FedericoCampanelliPoli/V-SoM/PCB/Ethernet.kicad_sch

## KiCad design PCB/Ethernet.kicad_sch (2026-02-23)

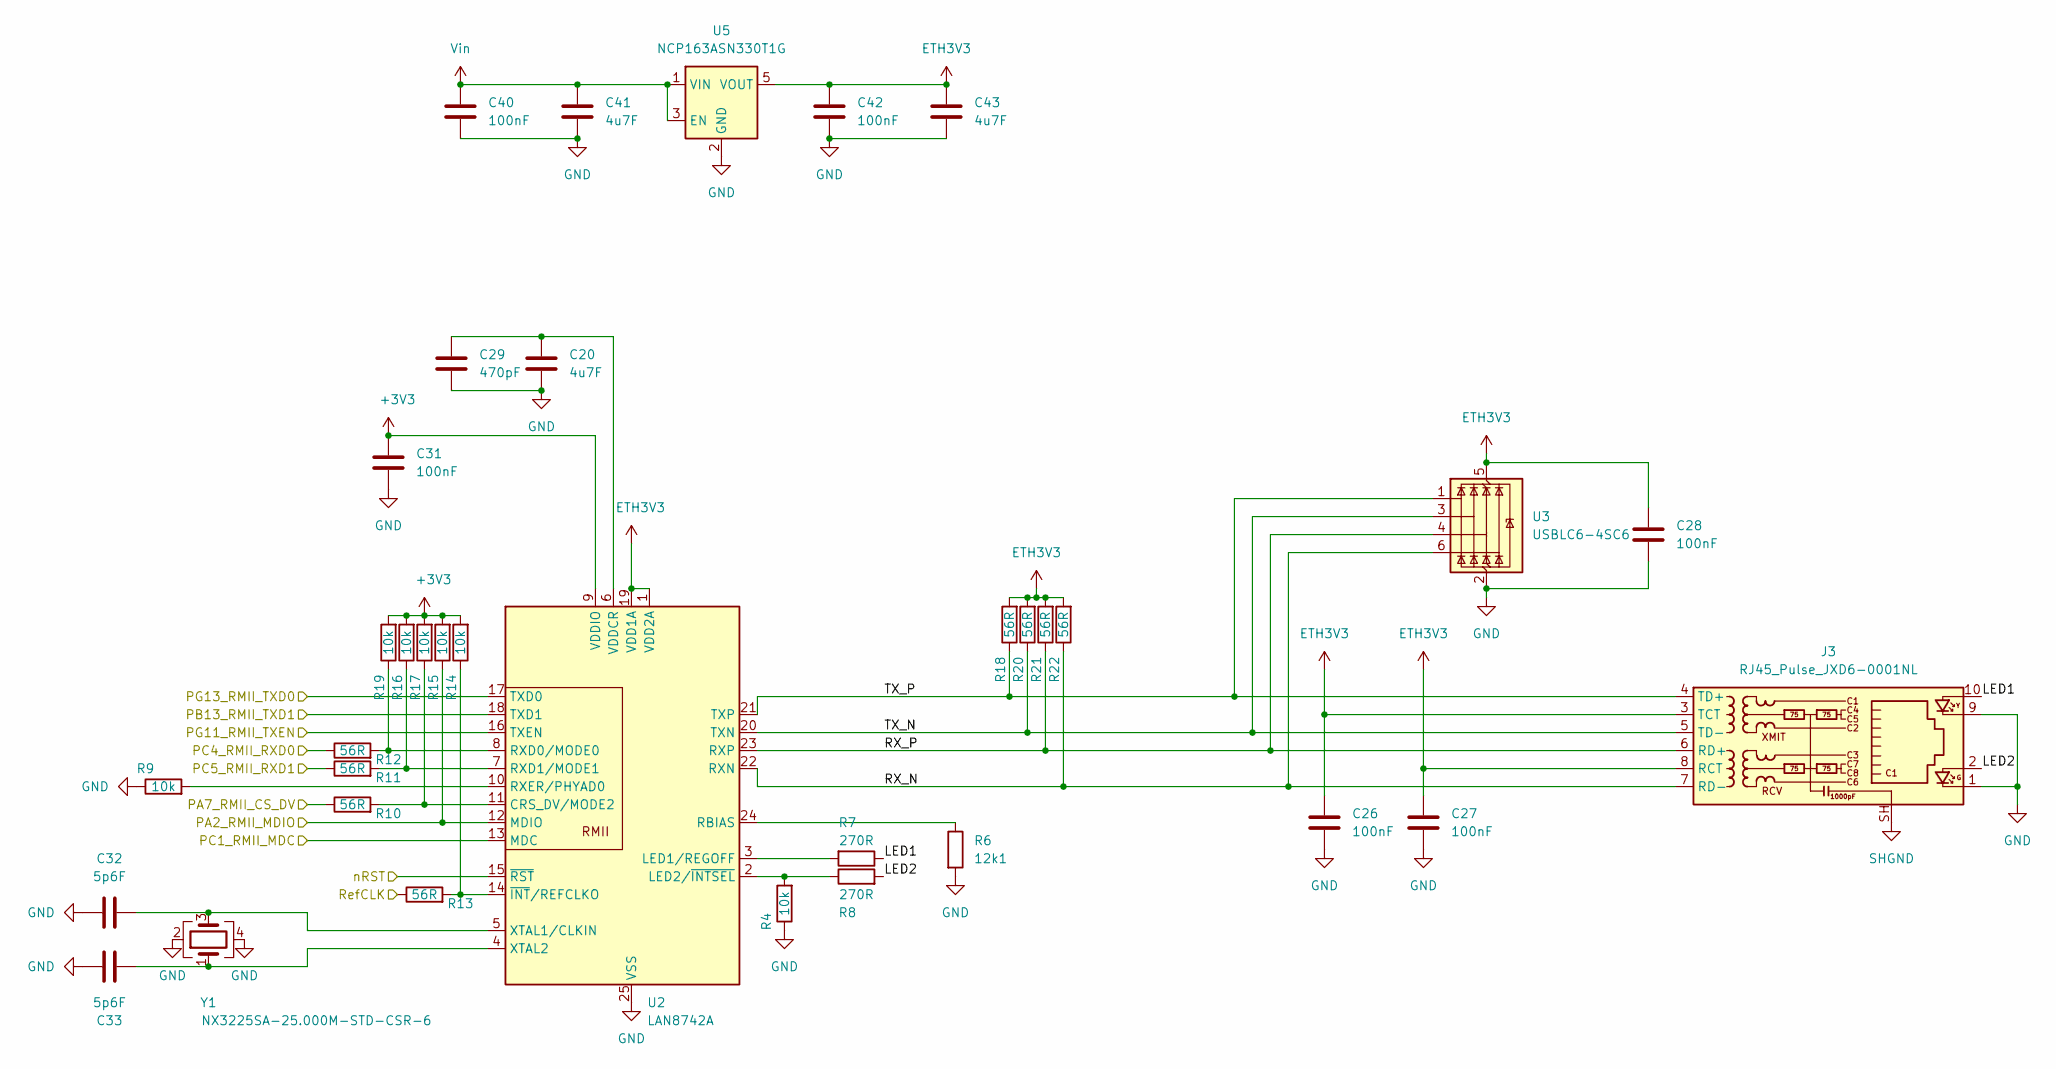
[picture p5: schematic Ethernet.kicad_sch]

Parts:
C20, C41, C43: 4u7F; C_0603_1608Metric; Manufacturer_Part_Number GRM188R61E475KE11D; Digikey PartNumber 490-7203-1-ND
C26, C27, C28, C31, C40, C42: 100nF; C_0603_1608Metric; Manufacturer_Part_Number C0603C104K5RACTU; Digikey PartNumber 399-C0603C104K5RACTUCT-ND
C29: 470pF; C_0603_1608Metric; Manufacturer_Part_Number C0603C471K5RACTU; Digikey PartNumber 399-C0603C471K5RACTUCT-ND
C32, C33: 5p6F; C_0603_1608Metric; Manufacturer_Part_Number C0603C569C5GACTU; Digikey PartNumber 399-C0603C569C5GACTUCT-ND
J3: RJ45_Pulse_JXD6-0001NL; RJ45_Pulse_JXD6-0001NL_Horizontal; Manufacturer_Part_Number JXD6-0001NL; Digikey PartNumber 553-JXD6-0001NLTCT-ND
R4, R9, R14, R15, R16, R17, R19: 10k; R_0603_1608Metric; Manufacturer_Part_Number RC0603FR-0710KL; Digikey PartNumber 311-10.0KHRCT-ND
R6: 12k1; R_0603_1608Metric; Manufacturer_Part_Number CRCW060312K1FKEAC; Digikey PartNumber 541-5158-1-ND
R7, R8: 270R; R_0603_1608Metric; Manufacturer_Part_Number RMCF0603FT270R; Digikey PartNumber RMCF0603FT270RCT-ND
R10, R11, R12, R13, R18, R20, R21, R22: 56R; R_0603_1608Metric; Manufacturer_Part_Number RC0603FR-0756RL; Digikey PartNumber 311-56.0HRCT-ND
U2: LAN8742A; VQFN-24-1EP_4x4mm_P0.5mm_EP2.5x2.5mm; Manufacturer_Part_Number LAN8742A-CZ; Digikey PartNumber LAN8742A-CZ-ND
U3: USBLC6-4SC6; SOT-23-6; Manufacturer_Part_Number USBLC6-4SC6; Digikey PartNumber 497-4492-1-ND
U5: NCP163ASN330T1G; SOT-23-5; Manufacturer_Part_Number NCP163ASN330T1G; Digikey PartNumber NCP163ASN330T1GOSCT-ND
Y1: NX3225SA-25.000M-STD-CSR-6; Oscillator_SMD_Abracon_ASE-4Pin_3.2x2.5mm; Manufacturer_Part_Number NX3225SA-25.000M-STD-CSR-6; Digikey PartNumber 644-STDCQR1-25MCT-ND

Connections:
+3V3: C31.1, R14.2, R15.2, R16.2, R17.2, R19.2, U2.9 (VDDIO)
ETH3V3: C26.1, C27.1, C28.1, C42.1, C43.1, J3.3 (TCT), J3.8 (RCT), R18.2, R20.2, R21.2, R22.2, U2.1 (VDD2A), U2.19 (VDD1A), U3.5 (VBUS), U5.5 (VOUT)
GND: C20.2, C26.2, C27.2, C28.2, C29.2, C31.2, C32.2, C33.2, C40.2, C41.2, C42.2, C43.2, J3.1, J3.9, R4.1, R6.2, R9.1, U2.25 (VSS), U3.2 (GND), U5.2 (GND), Y1.2, Y1.4
LED1: J3.10, R7.1
LED2: J3.2, R8.2
unnamed: C20.1, C29.1, U2.6 (VDDCR)
unnamed: C32.1, U2.5 (XTAL1/CLKIN), Y1.3
unnamed: C33.1, U2.4 (XTAL2), Y1.1
unnamed: R4.2, R8.1, U2.2 (LED2/~INTSEL)
unnamed: R6.1, U2.24 (RBIAS)
unnamed: R7.2, U2.3 (LED1/REGOFF)
unnamed: R9.2, U2.10 (RXER/PHYAD0)
unnamed: R10.2, R17.1, U2.11 (CRS_DV/MODE2)
unnamed: R11.2, R16.1, U2.7 (RXD1/MODE1)
unnamed: R12.2, R19.1, U2.8 (RXD0/MODE0)
unnamed: R13.2, R14.1, U2.14 (~INT/REFCLKO)
PA2_RMII_MDIO: R15.1, U2.12 (MDIO)
PA7_RMII_CS_DV: R10.1
PB13_RMII_TXD1: U2.18 (TXD1)
PC1_RMII_MDC: U2.13 (MDC)
PC4_RMII_RXD0: R12.1
PC5_RMII_RXD1: R11.1
PG11_RMII_TXEN: U2.16 (TXEN)
PG13_RMII_TXD0: U2.17 (TXD0)
RX_N: J3.7 (RD-), R22.1, U2.22 (RXN), U3.6 (I/O4)
RX_P: J3.6 (RD+), R21.1, U2.23 (RXP), U3.4 (I/O3)
RefCLK: R13.1
SHGND: J3.SH
TX_N: J3.5 (TD-), R20.1, U2.20 (TXN), U3.3 (I/O2)
TX_P: J3.4 (TD+), R18.1, U2.21 (TXP), U3.1 (I/O1)
Vin: C40.1, C41.1, U5.1 (VIN), U5.3 (EN)
nRST: U2.15 (~RST)
