FedericoCampanelliPoli/V-SoM/PCB/Power_Supply.kicad_sch

## KiCad design PCB/Power_Supply.kicad_sch (2026-02-23)

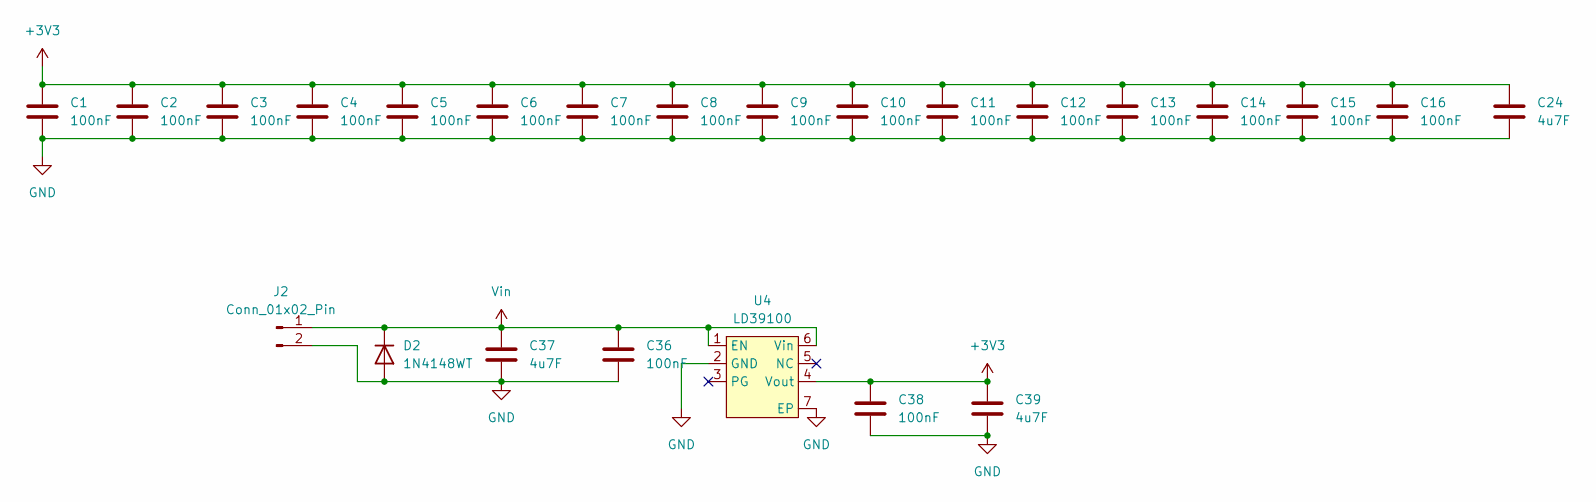
[picture p6: schematic Power_Supply.kicad_sch]

Parts:
C1, C2, C3, C4, C5, C6, C7, C8, C9, C10, C11, C12, C13, C14, C15, C16, C36, C38: 100nF; C_0603_1608Metric; Manufacturer_Part_Number C0603C104K5RACTU; Digikey PartNumber 399-C0603C104K5RACTUCT-ND
C24, C37, C39: 4u7F; C_0603_1608Metric; Manufacturer_Part_Number GRM188R61E475KE11D; Digikey PartNumber 490-7203-1-ND
D2: 1N4148WT; D_SOD-523; Manufacturer_Part_Number 1N4148WT; Digikey PartNumber 1N4148WTCT-ND
J2: Conn_01x02_Pin; PinHeader_1x02_P1.00mm_Vertical_SMD_Pin1Left; Manufacturer_Part_Number BC032-02-A-2-0200-0200-L-B; Digikey PartNumber 2073-BC032-02-A-2-0200-0200-L-BCT-ND
U4: LD39100; Maxim_TDFN-6-1EP_3x3mm_P0.95mm_EP1.5x2.3mm; Manufacturer_Part_Number LD39100PU33R; Digikey PartNumber 497-17047-1-ND

Connections:
+3V3: C1.1, C2.1, C3.1, C4.1, C5.1, C6.1, C7.1, C8.1, C9.1, C10.1, C11.1, C12.1, C13.1, C14.1, C15.1, C16.1, C24.1, C38.1, C39.1, U4.4 (Vout)
GND: C1.2, C2.2, C3.2, C4.2, C5.2, C6.2, C7.2, C8.2, C9.2, C10.2, C11.2, C12.2, C13.2, C14.2, C15.2, C16.2, C24.2, C36.2, C37.2, C38.2, C39.2, D2.2 (A), J2.2, U4.2 (GND), U4.7 (EP)
Vin: C36.1, C37.1, D2.1 (K), J2.1, U4.1 (EN), U4.6 (Vin)
