FedericoCampanelliPoli/V-SoM/PCB/uC.kicad_sch

## KiCad design PCB/uC.kicad_sch (2026-02-23)

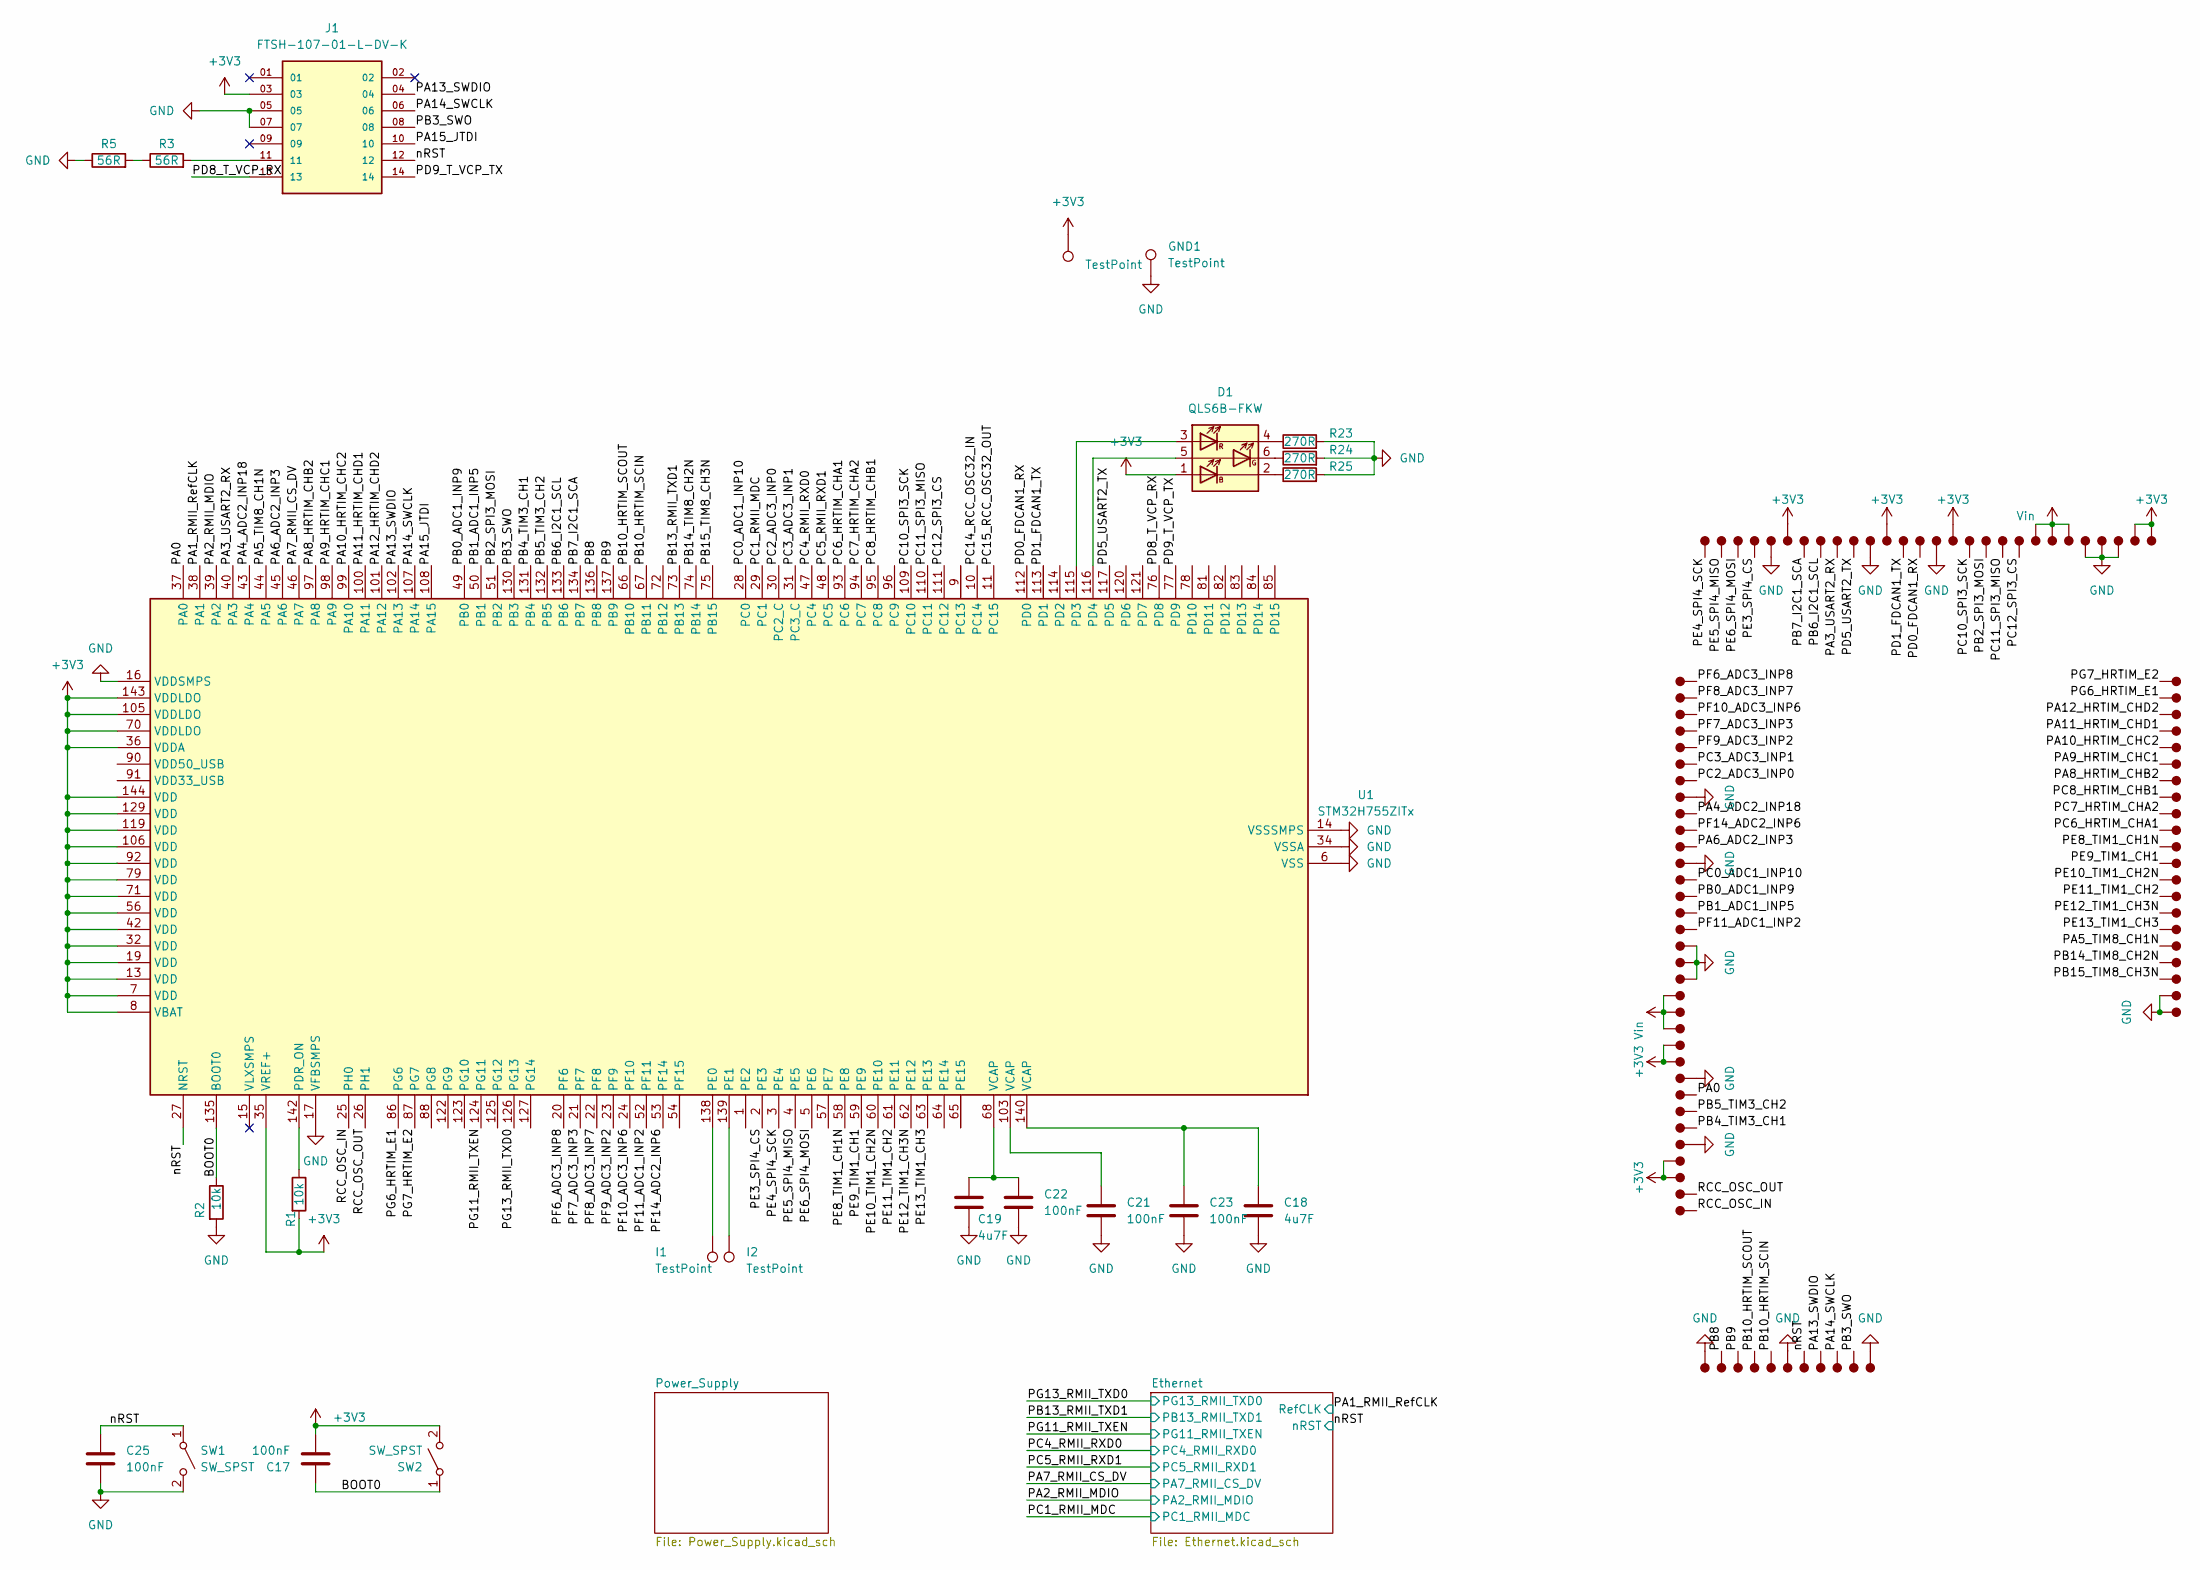
[picture p7: schematic uC.kicad_sch]

Parts:
3V3: TestPoint; TestPoint_Pad_D1.0mm; Manufacturer_Part_Number NA
C17, C21, C22, C23, C25: 100nF; C_0603_1608Metric; Manufacturer_Part_Number C0603C104K5RACTU; Digikey PartNumber 399-C0603C104K5RACTUCT-ND
C18, C19: 4u7F; C_0603_1608Metric; Manufacturer_Part_Number GRM188R61E475KE11D; Digikey PartNumber 490-7203-1-ND
D1: QLS6B-FKW; LED_Cree-PLCC6_4.7x1.5mm; Manufacturer_Part_Number QLS6B-FKW-CNSNSF043; Digikey PartNumber QLS6B-FKW-CNSNSF043CT-ND
GND1: TestPoint; TestPoint_Pad_D1.0mm; Manufacturer_Part_Number NA
I1, I2: TestPoint; TestPoint_Pad_D1.0mm; Manufacturer_Part_Number NA
J1: FTSH-107-01-L-DV-K; SAMTEC_FTSH-107-01-L-DV-K; PARTREV R; Digikey PartNumber SAM9449-ND
R1, R2: 10k; R_0603_1608Metric; Manufacturer_Part_Number RC0603FR-0710KL; Digikey PartNumber 311-10.0KHRCT-ND
R3, R5: 56R; R_0603_1608Metric; Manufacturer_Part_Number RC0603FR-0756RL; Digikey PartNumber 311-56.0HRCT-ND
R23, R24, R25: 270R; R_0603_1608Metric; Manufacturer_Part_Number RMCF0603FT270R; Digikey PartNumber RMCF0603FT270RCT-ND
SW1, SW2: SW_SPST; SW_Push_1P1T_NO_Vertical_Wuerth_434133025816; Manufacturer_Part_Number 434133025816; Digikey PartNumber 732-13663-1-ND
U1: STM32H755ZITx; LQFP-144_20x20mm_P0.5mm; Manufacturer_Part_Number STM32H755ZIT6; Digikey PartNumber STM32H755ZIT6-ND
U6, U7, U8, U9, U10, U11, U12, U13, U14, U15, U16, U17, U18, U19, U20, U21, U22, U23, U24, U25, U26, U27, U28, U29, U30, U31, U32, U33, U34, U35, U36, U37, U38, U39, U40, U41, U42, U43, U44, U45, U46, U47, U48, U49, U50, U51, U52, U53, U54, U55, U56, U57, U58, U59, U60, U61, U62, U63, U64, U65, U66, U67, U68, U69, U70, U71, U72, U73, U74, U75, U76, U77, U78, U79, U80, U81, U82, U83, U84, U85, U86, U87, U88, U89, U90, U91, U92, U93, U94, U95, U96, U97, U98: Castellation

Connections:
+3V3: 3V3.1, C17.2, D1.1 (AB), J1.03, R1.2, SW2.2 (B), U1.7 (VDD), U1.8 (VBAT), U1.13 (VDD), U1.19 (VDD), U1.32 (VDD), U1.35 (VREF+), U1.36 (VDDA), U1.42 (VDD), U1.56 (VDD), U1.70 (VDDLDO), U1.71 (VDD), U1.79 (VDD), U1.92 (VDD), U1.105 (VDDLDO), U1.106 (VDD), U1.119 (VDD), U1.129 (VDD), U1.143 (VDDLDO), U1.144 (VDD), U42.1, U45.1, U46.1, U48.1, U49.1, U53.1, U54.1, U55.1, U56.1
BOOT0: C17.1, R2.1, SW2.1 (A), U1.135 (BOOT0)
GND: C18.2, C19.2, C21.2, C22.2, C23.2, C25.2, GND1.1, J1.05, J1.07, R2.2, R5.1, R23.2, R24.2, R25.2, SW1.2 (B), U1.6 (VSS), U1.12 (VSS), U1.14 (VSSSMPS), U1.16 (VDDSMPS), U1.17 (VFBSMPS), U1.18 (VSS), U1.33 (VSS), U1.34 (VSSA), U1.41 (VSS), U1.55 (VSS), U1.69 (VSS), U1.80 (VSS), U1.89 (VSS), U1.104 (VSS), U1.118 (VSS), U1.128 (VSS), U1.141 (VSS), U33.1, U34.1, U35.1, U36.1, U37.1, U38.1, U39.1, U40.1, U41.1, U43.1, U44.1, U52.1, U85.1, U86.1, U87.1, U92.1, U93.1, U98.1
unnamed: C18.1, C23.1, U1.140 (VCAP)
unnamed: C19.1, C22.1, U1.68 (VCAP)
unnamed: C21.1, U1.103 (VCAP)
unnamed: D1.2 (KB), R25.1
unnamed: D1.3 (AR), U1.115 (PD3)
unnamed: D1.4 (KR), R23.1
unnamed: D1.5 (AG), U1.116 (PD4)
unnamed: D1.6 (KR), R24.1
unnamed: I1.1, U1.138 (PE0)
unnamed: I2.1, U1.139 (PE1)
unnamed: J1.11, R3.2
unnamed: R1.1, U1.142 (PDR_ON)
unnamed: R3.1, R5.2
PA0: U1.37 (PA0), U51.1
PA1_RMII_RefCLK: U1.38 (PA1)
PA2_RMII_MDIO: U1.39 (PA2)
PA3_USART2_RX: U1.40 (PA3), U25.1
PA4_ADC2_INP18: U1.43 (PA4), U75.1
PA5_TIM8_CH1N: U1.44 (PA5), U22.1
PA6_ADC2_INP3: U1.45 (PA6), U73.1
PA7_RMII_CS_DV: U1.46 (PA7)
PA8_HRTIM_CHB2: U1.97 (PA8), U9.1
PA9_HRTIM_CHC1: U1.98 (PA9), U10.1
PA10_HRTIM_CHC2: U1.99 (PA10), U11.1
PA11_HRTIM_CHD1: U1.100 (PA11), U12.1
PA12_HRTIM_CHD2: U1.101 (PA12), U13.1
PA13_SWDIO: J1.04, U1.102 (PA13), U94.1
PA14_SWCLK: J1.06, U1.107 (PA14), U95.1
PA15_JTDI: J1.10, U1.108 (PA15)
PB0_ADC1_INP9: U1.49 (PB0), U71.1
PB1_ADC1_INP5: U1.50 (PB1), U70.1
PB2_SPI3_MOSI: U1.51 (PB2), U60.1
PB3_SWO: J1.08, U1.130 (PB3), U96.1
PB4_TIM3_CH1: U1.131 (PB4), U47.1
PB5_TIM3_CH2: U1.132 (PB5), U50.1
PB6_I2C1_SCL: U1.133 (PB6), U27.1
PB7_I2C1_SCA: U1.134 (PB7), U28.1
PB8: U1.136 (PB8), U88.1
PB9: U1.137 (PB9), U89.1
PB10_HRTIM_SCIN: U1.67 (PB11), U91.1
PB10_HRTIM_SCOUT: U1.66 (PB10), U90.1
PB13_RMII_TXD1: U1.73 (PB13)
PB14_TIM8_CH2N: U1.74 (PB14), U23.1
PB15_TIM8_CH3N: U1.75 (PB15), U24.1
PC0_ADC1_INP10: U1.28 (PC0), U72.1
PC1_RMII_MDC: U1.29 (PC1)
PC2_ADC3_INP0: U1.30 (PC2_C), U76.1
PC3_ADC3_INP1: U1.31 (PC3_C), U77.1
PC4_RMII_RXD0: U1.47 (PC4)
PC5_RMII_RXD1: U1.48 (PC5)
PC6_HRTIM_CHA1: U1.93 (PC6), U6.1
PC7_HRTIM_CHA2: U1.94 (PC7), U7.1
PC8_HRTIM_CHB1: U1.95 (PC8), U8.1
PC10_SPI3_SCK: U1.109 (PC10), U58.1
PC11_SPI3_MISO: U1.110 (PC11), U59.1
PC12_SPI3_CS: U1.111 (PC12), U57.1
PC14_RCC_OSC32_IN: U1.10 (PC14)
PC15_RCC_OSC32_OUT: U1.11 (PC15)
PD0_FDCAN1_RX: U1.112 (PD0), U62.1
PD1_FDCAN1_TX: U1.113 (PD1), U61.1
PD5_USART2_TX: U1.117 (PD5), U26.1
PD8_T_VCP_RX: J1.13, U1.76 (PD8)
PD9_T_VCP_TX: J1.14, U1.77 (PD9)
PE3_SPI4_CS: U1.2 (PE3), U29.1
PE4_SPI4_SCK: U1.3 (PE4), U30.1
PE5_SPI4_MISO: U1.4 (PE5), U31.1
PE6_SPI4_MOSI: U1.5 (PE6), U32.1
PE8_TIM1_CH1N: U1.58 (PE8), U17.1
PE9_TIM1_CH1: U1.59 (PE9), U16.1
PE10_TIM1_CH2N: U1.60 (PE10), U19.1
PE11_TIM1_CH2: U1.61 (PE11), U18.1
PE12_TIM1_CH3N: U1.62 (PE12), U21.1
PE13_TIM1_CH3: U1.63 (PE13), U20.1
PF6_ADC3_INP8: U1.20 (PF6), U82.1
PF7_ADC3_INP3: U1.21 (PF7), U79.1
PF8_ADC3_INP7: U1.22 (PF8), U81.1
PF9_ADC3_INP2: U1.23 (PF9), U78.1
PF10_ADC3_INP6: U1.24 (PF10), U80.1
PF11_ADC1_INP2: U1.52 (PF11), U69.1
PF14_ADC2_INP6: U1.53 (PF14), U74.1
PG6_HRTIM_E1: U1.86 (PG6), U14.1
PG7_HRTIM_E2: U1.87 (PG7), U15.1
PG11_RMII_TXEN: U1.124 (PG11)
PG13_RMII_TXD0: U1.126 (PG13)
RCC_OSC_IN: U1.25 (PH0), U84.1
RCC_OSC_OUT: U1.26 (PH1), U83.1
Vin: U63.1, U64.1, U65.1, U66.1, U67.1, U68.1
nRST: C25.1, J1.12, SW1.1 (A), U1.27 (NRST), U97.1
